Thunderbird2086/OmniCode-9001/img/layout/omnicode-9001-colemak-dh.png

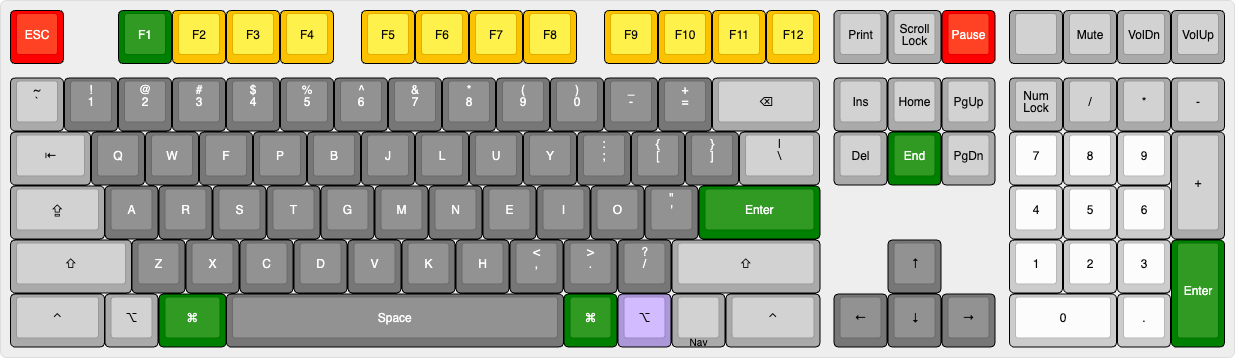
img/layout/omnicode-9001-colemak-dh.png
