Thunderbird2086/OmniCode-9001/3D Models/PhaseShift_Plate.step

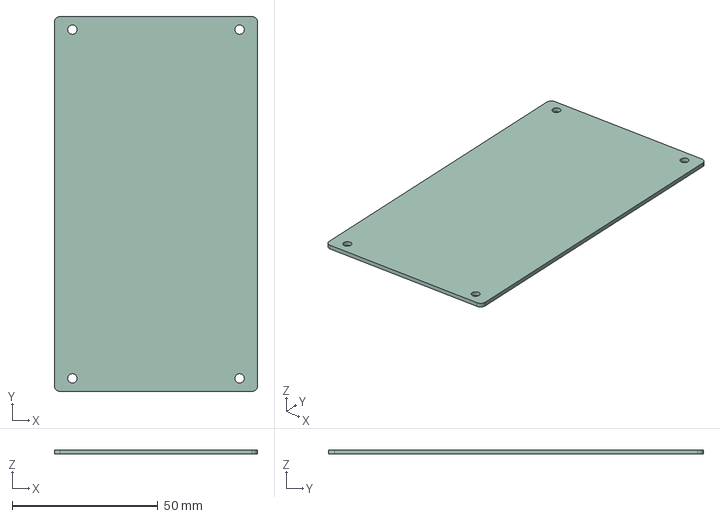
[picture p32: CAD file, 2025-07-11]
3D Models/PhaseShift_Plate.step
69.8 x 128.6 x 1.51 mm
